MagicTINTIN/ChrisKeyboards/doc/connector/conn_kbd.jpg

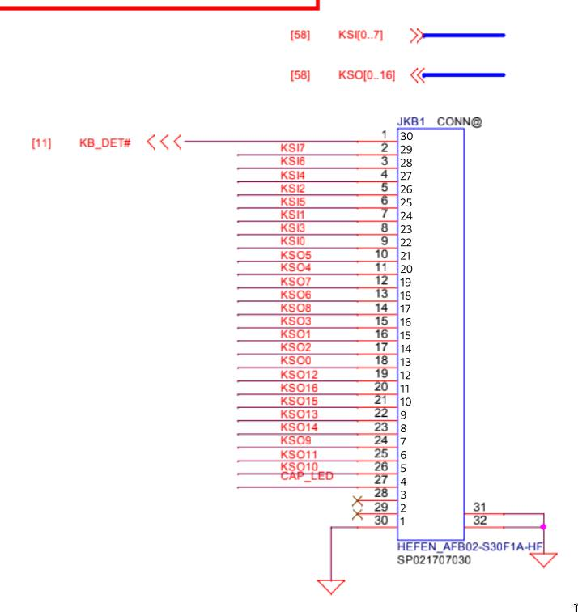
doc/connector/conn_kbd.jpg
