MagicTINTIN/ChrisKeyboards/doc/dell2merde/39-ced2846b18.jpg

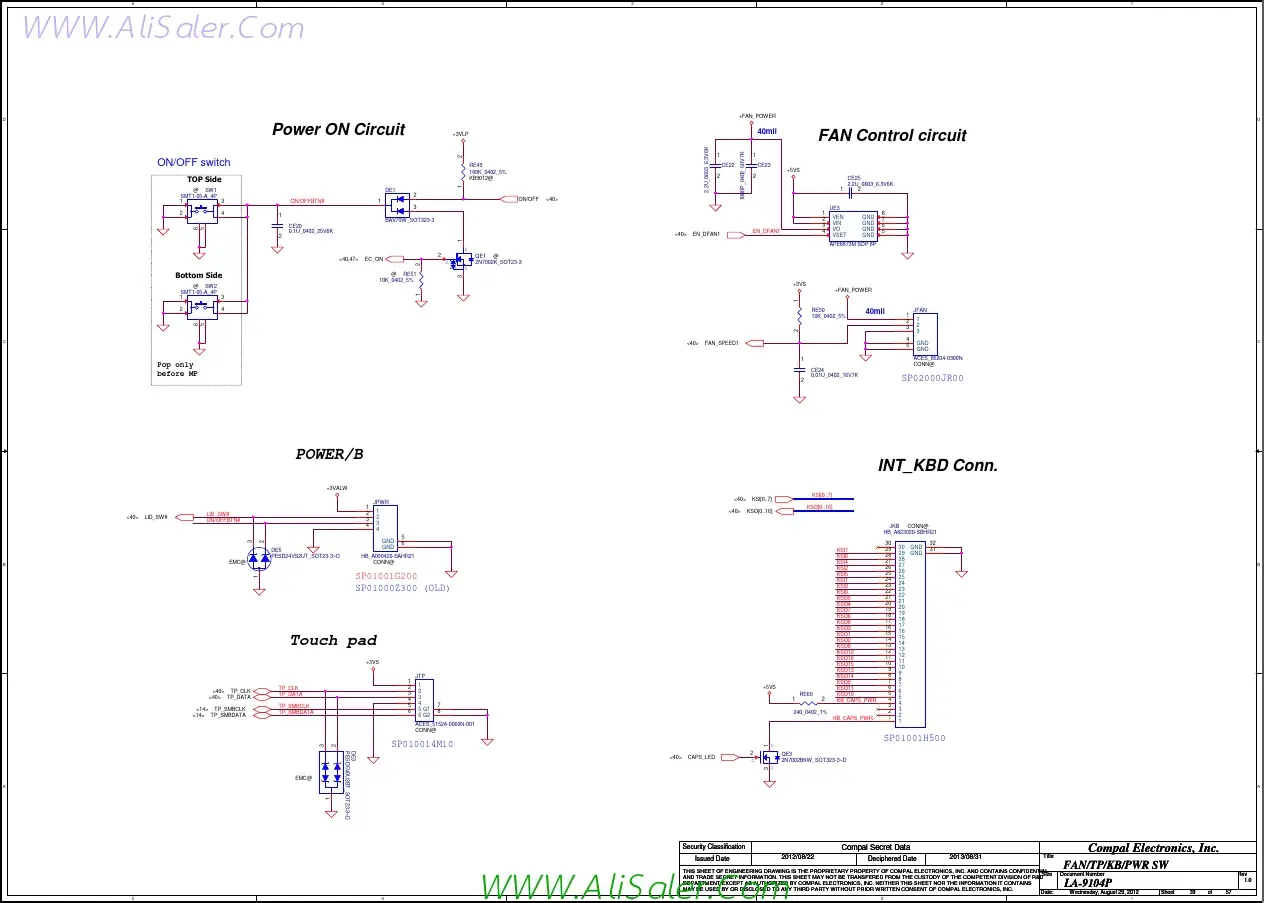
doc/dell2merde/39-ced2846b18.jpg
